davemuscle/96band_msa/lcd/lcd_top.xdc

set_property PACKAGE_PIN M3 [get_ports {lcd_db[15]}]
set_property IOSTANDARD LVCMOS33 [get_ports {lcd_db[15]}]
set_property PACKAGE_PIN L3 [get_ports {lcd_db[14]}]
set_property IOSTANDARD LVCMOS33 [get_ports {lcd_db[14]}]
set_property PACKAGE_PIN A16 [get_ports {lcd_db[13]}]
set_property IOSTANDARD LVCMOS33 [get_ports {lcd_db[13]}]
set_property PACKAGE_PIN K3 [get_ports {lcd_db[12]}]
set_property IOSTANDARD LVCMOS33 [get_ports {lcd_db[12]}]
set_property PACKAGE_PIN C15 [get_ports {lcd_db[11]}]
set_property IOSTANDARD LVCMOS33 [get_ports {lcd_db[11]}]
set_property PACKAGE_PIN H1 [get_ports {lcd_db[10]}]
set_property IOSTANDARD LVCMOS33 [get_ports {lcd_db[10]}]
set_property PACKAGE_PIN A15 [get_ports {lcd_db[9]}]
set_property IOSTANDARD LVCMOS33 [get_ports {lcd_db[9]}]
set_property PACKAGE_PIN B15 [get_ports {lcd_db[8]}]
set_property IOSTANDARD LVCMOS33 [get_ports {lcd_db[8]}]
set_property PACKAGE_PIN A14 [get_ports {lcd_db[7]}]
set_property IOSTANDARD LVCMOS33 [get_ports {lcd_db[7]}]
set_property PACKAGE_PIN J3 [get_ports {lcd_db[6]}]
set_property IOSTANDARD LVCMOS33 [get_ports {lcd_db[6]}]
set_property PACKAGE_PIN J1 [get_ports {lcd_db[5]}]
set_property IOSTANDARD LVCMOS33 [get_ports {lcd_db[5]}]
set_property PACKAGE_PIN K2 [get_ports {lcd_db[4]}]
set_property IOSTANDARD LVCMOS33 [get_ports {lcd_db[4]}]
set_property PACKAGE_PIN L1 [get_ports {lcd_db[3]}]
set_property IOSTANDARD LVCMOS33 [get_ports {lcd_db[3]}]
set_property PACKAGE_PIN L2 [get_ports {lcd_db[2]}]
set_property IOSTANDARD LVCMOS33 [get_ports {lcd_db[2]}]
set_property PACKAGE_PIN M1 [get_ports {lcd_db[1]}]
set_property IOSTANDARD LVCMOS33 [get_ports {lcd_db[1]}]
set_property PACKAGE_PIN N3 [get_ports {lcd_db[0]}]
set_property IOSTANDARD LVCMOS33 [get_ports {lcd_db[0]}]
set_property PACKAGE_PIN N2 [get_ports lcd_rst]
set_property IOSTANDARD LVCMOS33 [get_ports lcd_rst]
set_property PACKAGE_PIN N1 [get_ports lcd_wr]
set_property IOSTANDARD LVCMOS33 [get_ports lcd_wr]
set_property PACKAGE_PIN M2 [get_ports lcd_cs]
set_property IOSTANDARD LVCMOS33 [get_ports lcd_cs]
set_property PACKAGE_PIN P3 [get_ports lcd_rs]
set_property IOSTANDARD LVCMOS33 [get_ports lcd_rs]
