davemuscle/96band_msa/lcd/top.xdc

set_property IOSTANDARD LVCMOS33 [get_ports clk12M]
set_property IOSTANDARD LVCMOS33 [get_ports rst]

set_property PACKAGE_PIN A18 [get_ports rst]
set_property PACKAGE_PIN L17 [get_ports clk12M]

#PIN 48
#set_property PACKAGE_PIN V8 [get_ports ready]
#set_property IOSTANDARD LVCMOS33 [get_ports ready]

#PIN 47
#set_property PACKAGE_PIN U8 [get_ports valid]
#set_property IOSTANDARD LVCMOS33 [get_ports valid]
