davemuscle/96band_msa/vga/top.xdc

set_property IOSTANDARD LVCMOS33 [get_ports clk12M]
set_property PACKAGE_PIN L17 [get_ports clk12M]

#send locked to LD1
set_property IOSTANDARD LVCMOS33 [get_ports locked]
set_property PACKAGE_PIN A17 [get_ports locked]
